ammmec/eCal/eCal_PC/config/img/default.png

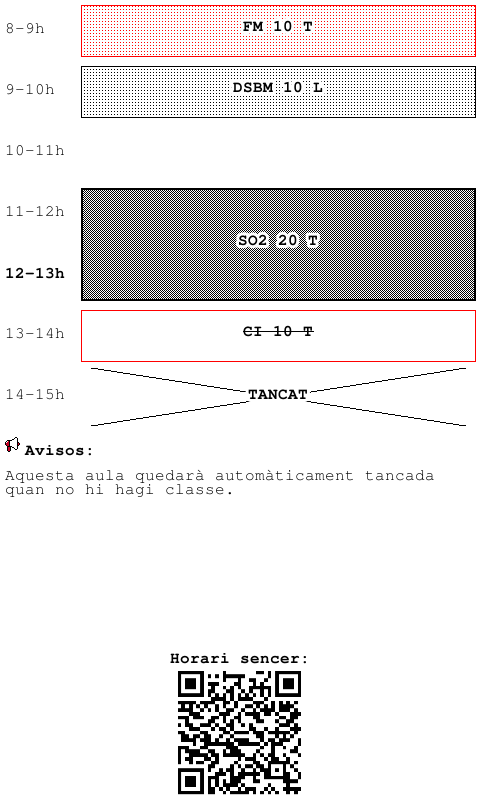
eCal_PC/config/img/default.png
