ammmec/eCal/eCal_PC/config/img/horizontal.png

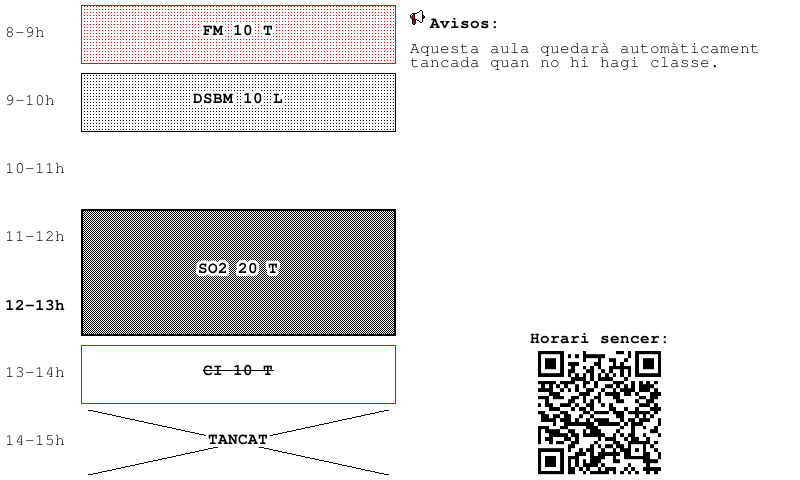
eCal_PC/config/img/horizontal.png
