ammmec/eCal/eCal_PC/config/img/horizontal_lines.png

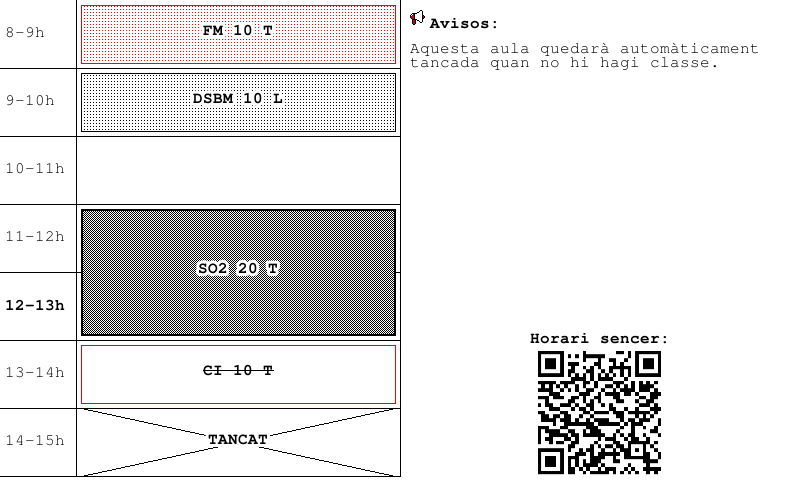
eCal_PC/config/img/horizontal_lines.png
