ammmec/eCal/raco/Racó de la FIB_fitxers/button.png

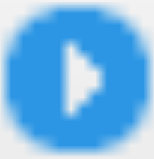
raco/Racó de la FIB_fitxers/button.png
