ammmec/eCal/eCal/schedule_bitmaps.h

#ifndef BITMAPS_H
#define BITMAPS_H
// 'qr', 125x125px
const unsigned char qr [] PROGMEM = {
	0x00, 0x00, 0x00, 0x00, 0x00, 0x00, 0x00, 0x00, 0x00, 0x00, 0x00, 0x00, 0x00, 0x00, 0x00, 0x00,
	0x7f, 0xff, 0xff, 0xe0, 0x00, 0x03, 0x80, 0x00, 0x00, 0x01, 0xfe, 0x1c, 0x3f, 0xff, 0xff, 0xf0,
	0x7f, 0xff, 0xff, 0xe0, 0x00, 0x03, 0x80, 0x00, 0x00, 0x01, 0xfe, 0x1c, 0x3f, 0xff, 0xff, 0xf0,
	0x7f, 0xff, 0xff, 0xe0, 0x00, 0x03, 0x80, 0x00, 0x00, 0x01, 0xfe, 0x1c, 0x3f, 0xff, 0xff, 0xf0,
	0x70, 0x00, 0x01, 0xe1, 0xc3, 0xc3, 0xff, 0xff, 0xf0, 0x00, 0x00, 0x1c, 0x3c, 0x00, 0x00, 0x70,
	0x70, 0x00, 0x01, 0xe1, 0xc3, 0xc3, 0xff, 0xff, 0xf0, 0x00, 0x00, 0x1c, 0x3c, 0x00, 0x00, 0x70,
	0x70, 0x00, 0x01, 0xe1, 0xc3, 0xc3, 0xff, 0xff, 0xf0, 0x00, 0x00, 0x1c, 0x3c, 0x00, 0x00, 0x70,
	0x70, 0x00, 0x01, 0xe1, 0xc3, 0xc3, 0xff, 0xff, 0xf0, 0x00, 0x00, 0x1c, 0x3c, 0x00, 0x00, 0x70,
	0x70, 0xff, 0xe1, 0xe0, 0x00, 0x03, 0x80, 0x07, 0x00, 0xfe, 0x01, 0xe0, 0x3c, 0x3f, 0xf8, 0x70,
	0x70, 0xff, 0xe1, 0xe0, 0x00, 0x03, 0x80, 0x07, 0x00, 0xfe, 0x01, 0xe0, 0x3c, 0x3f, 0xf8, 0x70,
	0x70, 0xff, 0xe1, 0xe0, 0x00, 0x03, 0x80, 0x07, 0x00, 0xfe, 0x01, 0xe0, 0x3c, 0x3f, 0xf8, 0x70,
	0x70, 0xff, 0xe1, 0xe0, 0x00, 0x03, 0x80, 0x07, 0x00, 0xfe, 0x01, 0xe0, 0x3c, 0x3f, 0xf8, 0x70,
	0x70, 0xff, 0xe1, 0xe1, 0xff, 0xc0, 0x00, 0x7f, 0x00, 0x0e, 0x1e, 0x00, 0x3c, 0x3f, 0xf8, 0x70,
	0x70, 0xff, 0xe1, 0xe1, 0xff, 0xc0, 0x00, 0x7f, 0x00, 0x0e, 0x1e, 0x00, 0x3c, 0x3f, 0xf8, 0x70,
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
	0x00, 0xaa, 0xaa, 0x00, 0x00, 0x00, 0x00, 0x00, 0x00, 0x00, 0x00, 0x00, 0x00, 0x00, 0x00, 0xff,
	0xfe, 0x00, 0x00, 0x00, 0x00, 0x00, 0x00, 0x00, 0x00, 0x00, 0x00, 0x00, 0x00, 0xaa, 0xaa, 0x00,
	0x00, 0x00, 0x00, 0x00, 0x00, 0x00, 0x00, 0x00, 0x00, 0x00, 0x00, 0xff, 0xfe, 0x00, 0x00, 0x00,
	0x00, 0x00, 0x00, 0x00, 0x00, 0x00, 0x00, 0x00, 0x00, 0xaa, 0xaa, 0x00, 0x00, 0x00, 0x00, 0x00,
	0x00, 0x00, 0x00, 0x00, 0x00, 0x00, 0x00, 0xff, 0xfe, 0x00, 0x00, 0x00, 0x00, 0x00, 0x00, 0x00,
	0x00, 0x00, 0x00, 0x00, 0x00, 0xaa, 0xaa, 0x00, 0x00, 0x00, 0x00, 0x00, 0x00, 0x00, 0x00, 0x00,
	0x00, 0x00, 0x00, 0xff, 0xfe, 0x00, 0x00, 0x00, 0x00, 0x00, 0x00, 0x00, 0x00, 0x00, 0x00, 0x00,
	0x00, 0xaa, 0xaa, 0x00, 0x00, 0x00, 0x00, 0x00, 0x00, 0x00, 0x00, 0x00, 0x00, 0x00, 0x00, 0xff,
	0xfe, 0x00, 0x00, 0x00, 0x00, 0x00, 0x00, 0x00, 0x00, 0x00, 0x00, 0x00, 0x00, 0xaa, 0xaa, 0x00,
	0x00, 0x00, 0x00, 0x00, 0x00, 0x00, 0x00, 0x00, 0x00, 0x00, 0x00, 0xff, 0xfe, 0x00, 0x00, 0x00,
	0x00, 0x00, 0x00, 0x00, 0x00, 0x00, 0x00, 0x00, 0x00, 0x00, 0x00, 0x00, 0x00, 0x00, 0x00, 0x00,
	0x00, 0x00
};

#endif // BITMAPS_H
